Kunalverma1502/esp32-mini-drone/IMAGES/IMG_0709.JPG

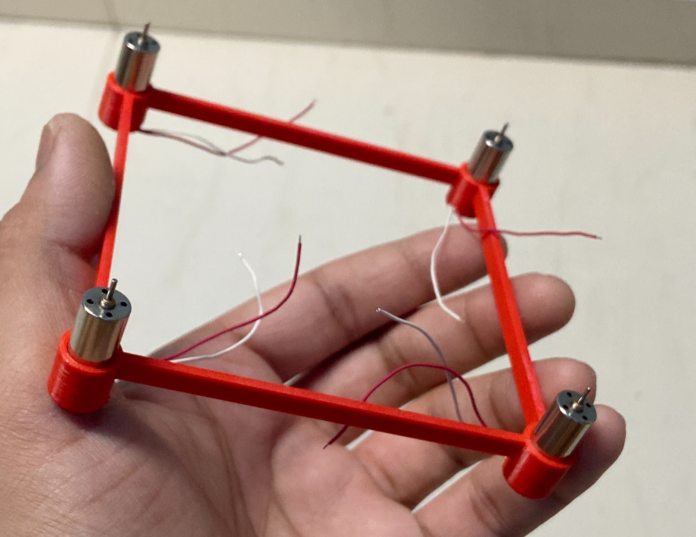
IMAGES/IMG_0709.JPG
