Kunalverma1502/esp32-mini-drone/IMAGES/IMG_0710.JPG

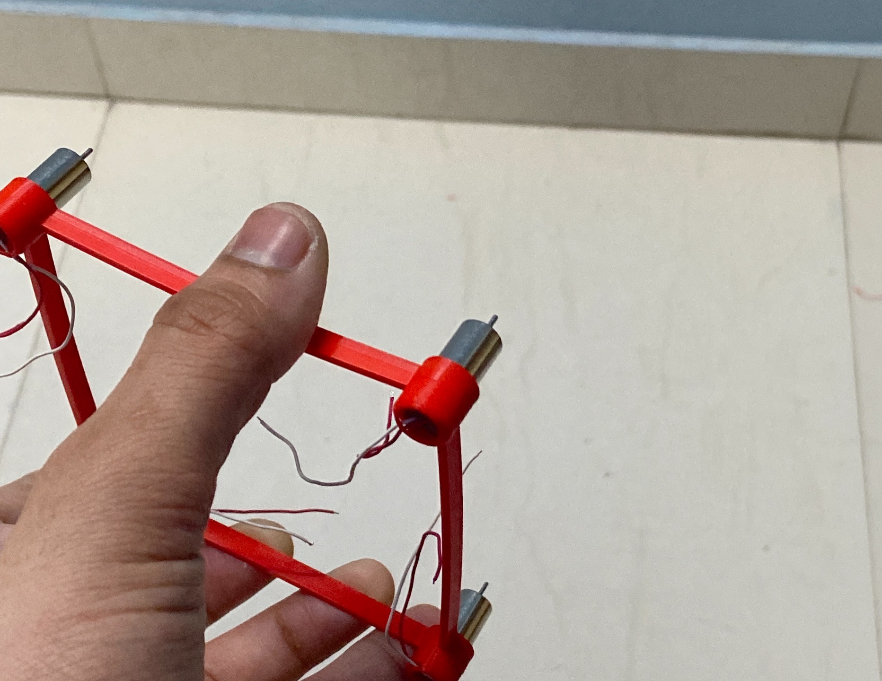
IMAGES/IMG_0710.JPG
