Kunalverma1502/esp32-mini-drone/IMAGES/IMG_0712.JPG

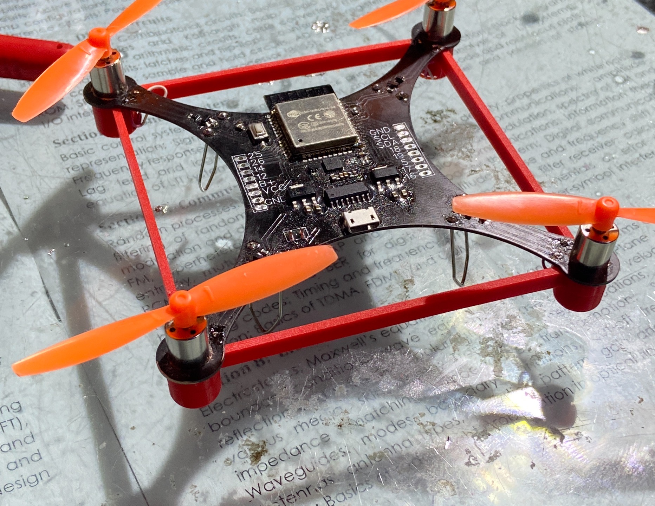
IMAGES/IMG_0712.JPG
